denis-gz/pw-meter/docs/hardware/jlcpcb_3d_2.png

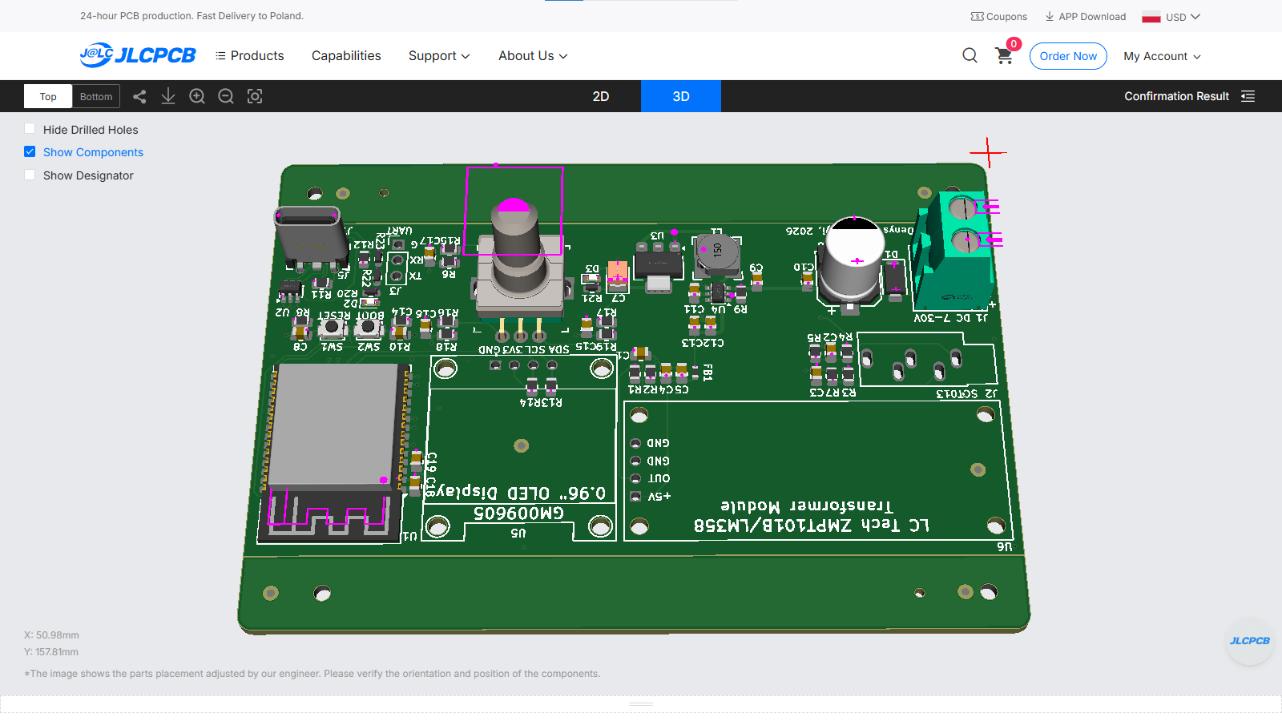
docs/hardware/jlcpcb_3d_2.png
