denis-gz/pw-meter/docs/hardware/PcbBottom.png

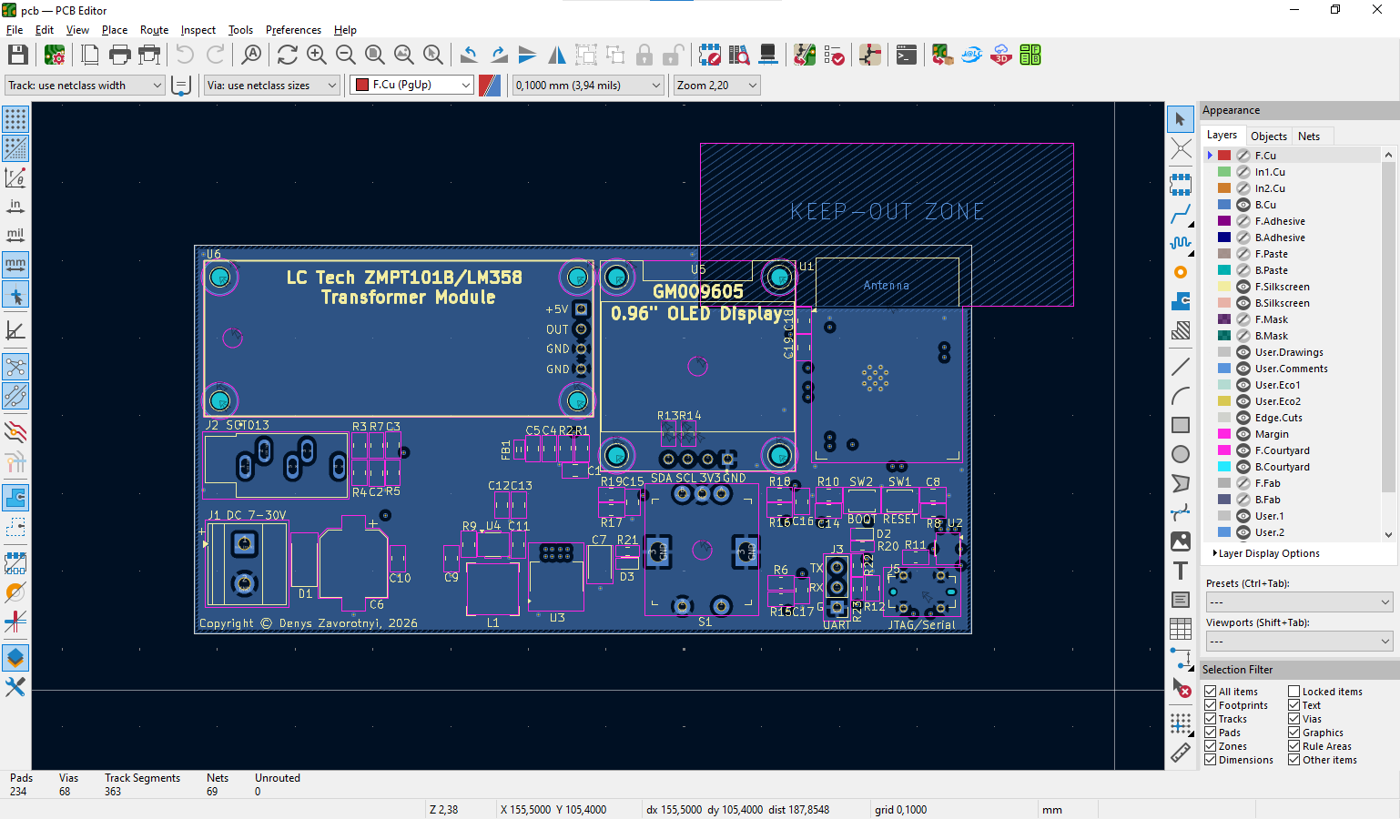
docs/hardware/PcbBottom.png
