denis-gz/pw-meter/main/Button.cpp

#include "Button.h"

#include <freertos/FreeRTOS.h>

#include <esp_timer.h>
#include <esp_log.h>

#include "common.h"

std::once_flag Button::s_isr_service_flag;

// How much time a pin should have the HIGH level to clear button depressed state
constexpr const int64_t HIGH_STATE_GUARD_INTERVAL_US = 10 * 1000LL;         // 10 ms
constexpr const int64_t HIGH_STATE_LONG_CLICK_INTERVAL_US = 350 * 1000LL;   // 350 ms


Button::Button(int pin, callback_t on_click)
{
    std::call_once(s_isr_service_flag, []() {
        esp_err_t err = gpio_install_isr_service(ESP_INTR_FLAG_IRAM);
        // Ignore the error if another module already installed it!
        if (err != ESP_OK && err != ESP_ERR_INVALID_STATE) {
            ESP_ERROR_CHECK(err);
        }
    });

    gpio_config_t gpio_conf = {
        .pin_bit_mask = 1ULL << pin,
        .mode         = GPIO_MODE_INPUT,
        .pull_up_en   = GPIO_PULLUP_ENABLE,
        .pull_down_en = GPIO_PULLDOWN_DISABLE,
        .intr_type    = GPIO_INTR_ANYEDGE,
    };

    m_pin = static_cast<gpio_num_t>(pin);
    ESP_ERROR_CHECK(gpio_config(&gpio_conf));
    ESP_ERROR_CHECK(gpio_isr_handler_add(m_pin, member_cast<gpio_isr_t>(&Button::handler), this));
    ESP_ERROR_CHECK(gpio_intr_enable(m_pin));
    m_on_click = on_click;

    gpio_pin_glitch_filter_config_t gl_conf = {
        .clk_src = GLITCH_FILTER_CLK_SRC_DEFAULT,
        .gpio_num = m_pin,
    };

    ESP_ERROR_CHECK(gpio_new_pin_glitch_filter(&gl_conf, &gl_handle));
    ESP_ERROR_CHECK(gpio_glitch_filter_enable(gl_handle));

    // Set appripriate defaults so we don't miss the first click
    int64_t now_time = esp_timer_get_time();
    m_depress_time = now_time;
    m_release_time = now_time;
    m_level = 1;
}

Button::~Button()
{
    if (m_pin != GPIO_NUM_NC) {
        gpio_reset_pin(m_pin);
        gpio_isr_handler_remove(m_pin);
    }
    if (gl_handle) {
        gpio_glitch_filter_disable(gl_handle);
        gpio_del_glitch_filter(gl_handle);
    }
}

void IRAM_ATTR Button::handler()
{
    int64_t now_time = esp_timer_get_time();
    int level = gpio_get_level(m_pin);

    // Check if pin level is unchanged
    if (m_level == level) {
        if (level)                  // High level - button remains released
            m_depress_time = 0;
        else                        // Low level - button remains depressed
            m_release_time = 0;
    }
    else {                          // Level changed
        if (level)
            m_release_time = now_time;
        else
            m_depress_time = now_time;
    }

    m_level = level;                // Store actual values
    m_sample_time = now_time;

    if (m_level == 1                // High level - button is released
        && m_depress_time           // Exclude consequtive depress or release events
        && m_release_time
        && m_release_time - m_depress_time > HIGH_STATE_GUARD_INTERVAL_US)
    {
        m_on_click(m_release_time - m_depress_time > HIGH_STATE_LONG_CLICK_INTERVAL_US);
    }
}
